ENSTABretagneRobotics/Ventilator/CAD/ToPrint/NormalNozzle/STL/Adapter_12x22mm_45deg.stl

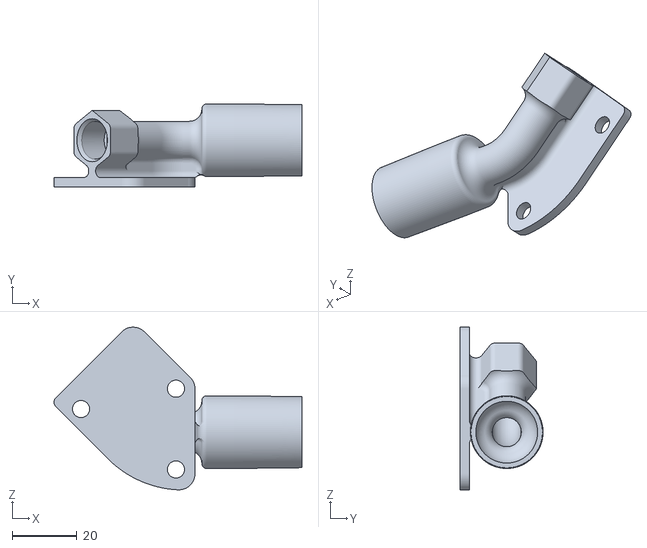
[picture p16: CAD file, 2020-05-25]
CAD/ToPrint/NormalNozzle/STL/Adapter_12x22mm_45deg.stl
76.7 x 25.8 x 50.3
